SteveRMann/Halloween-2022/Beach Video/Pirate Ship 1.png

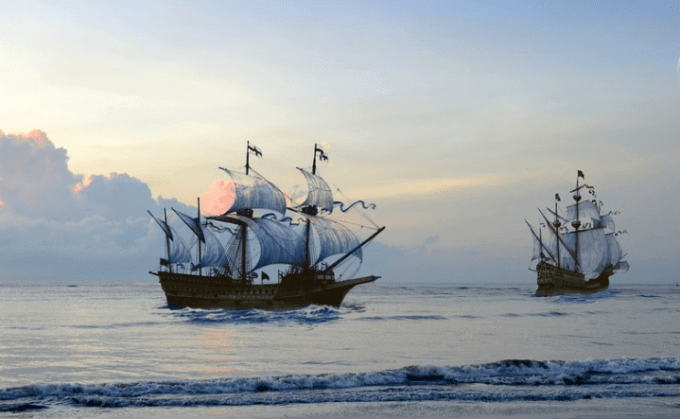
Beach Video/Pirate Ship 1.png
