SteveRMann/Halloween-2022/Beach Video/pirate-ship-blur.png

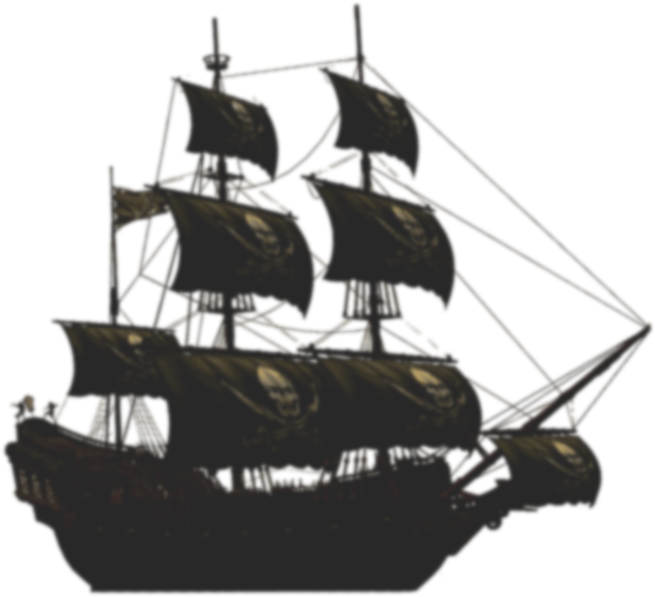
Beach Video/pirate-ship-blur.png
