SteveRMann/Halloween-2022/Beach Video/pirate-ship-transparent.png

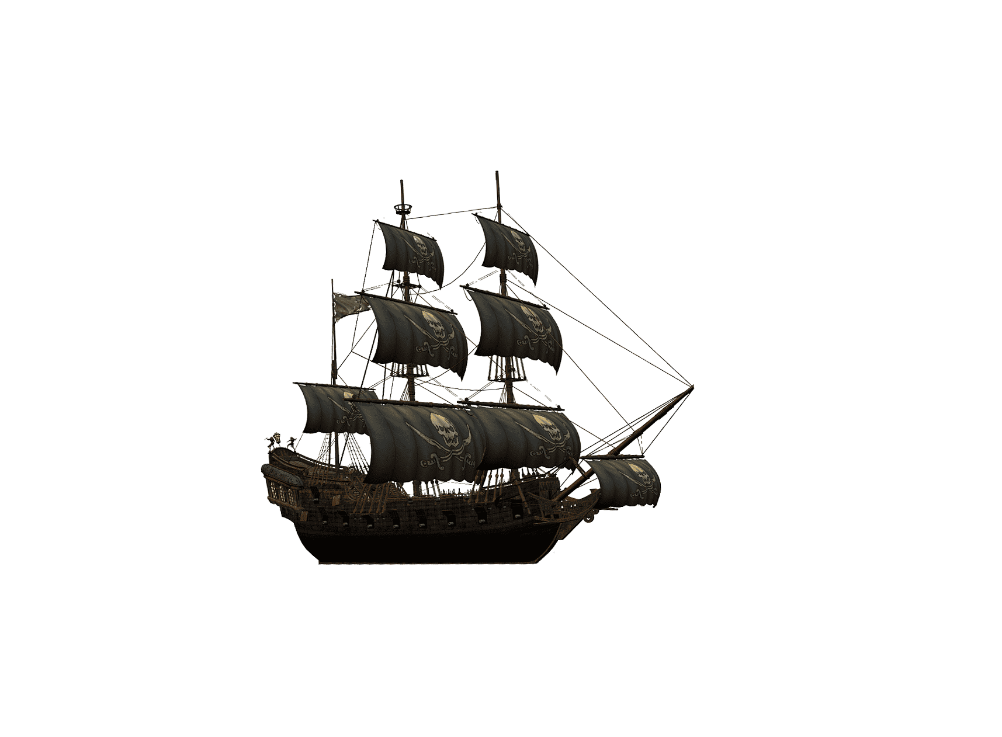
Beach Video/pirate-ship-transparent.png
