SteveRMann/Halloween-2022/Fan/board.jpg

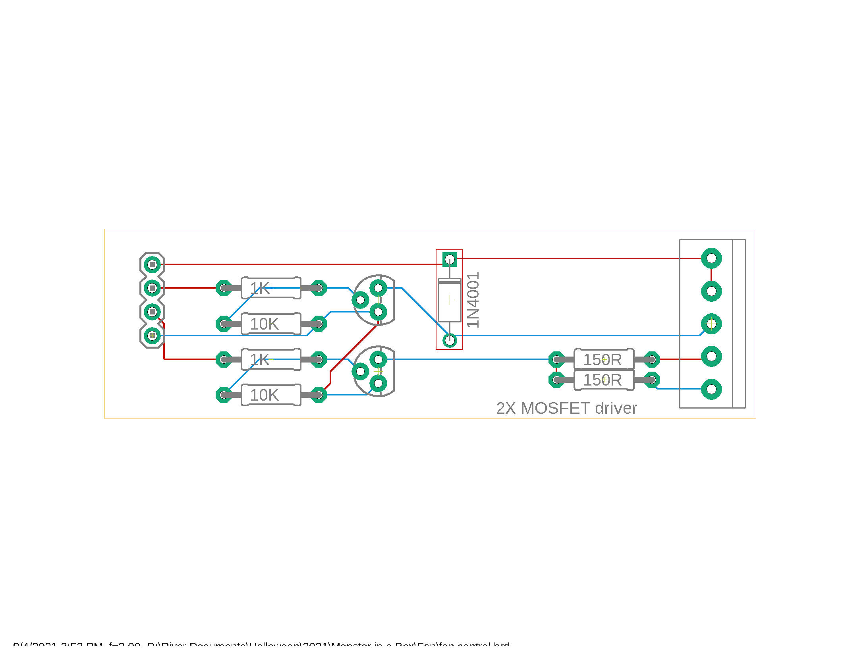
Fan/board.jpg
