SteveRMann/Halloween-2022/Lid Simulator/Fan Control- Monster Box.jpg

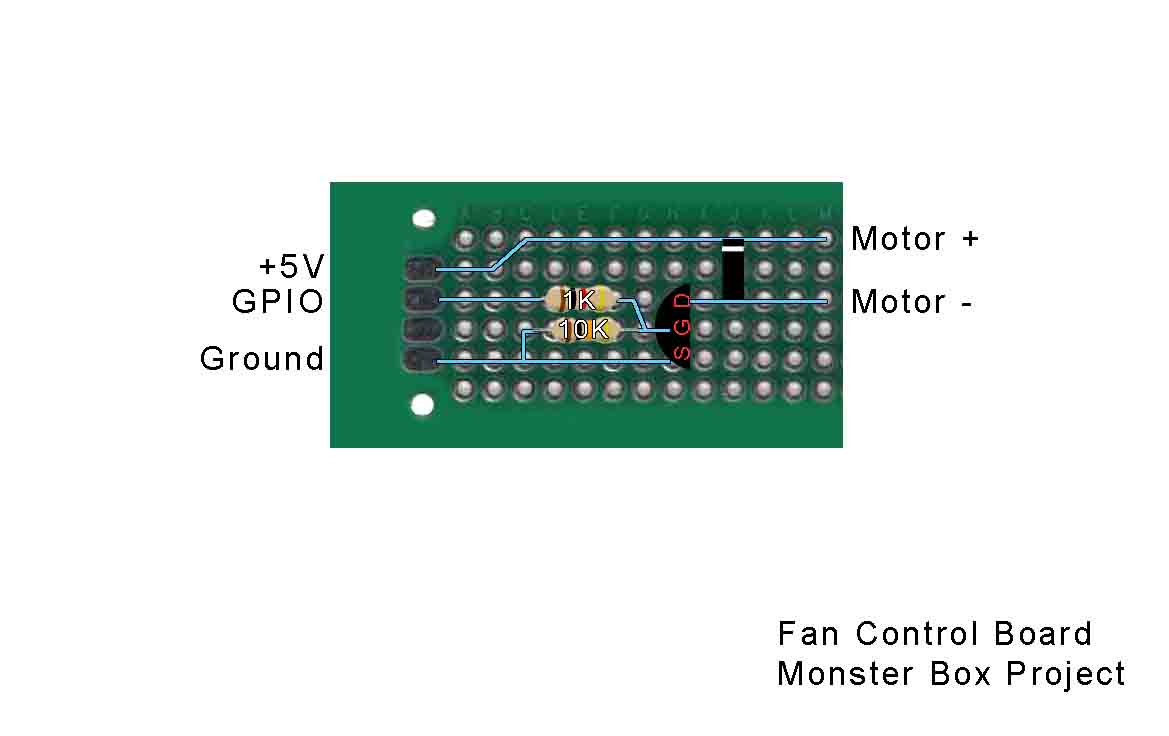
Lid Simulator/Fan Control- Monster Box.jpg
