SteveRMann/Halloween-2022/Lid Simulator/fan control.jpg

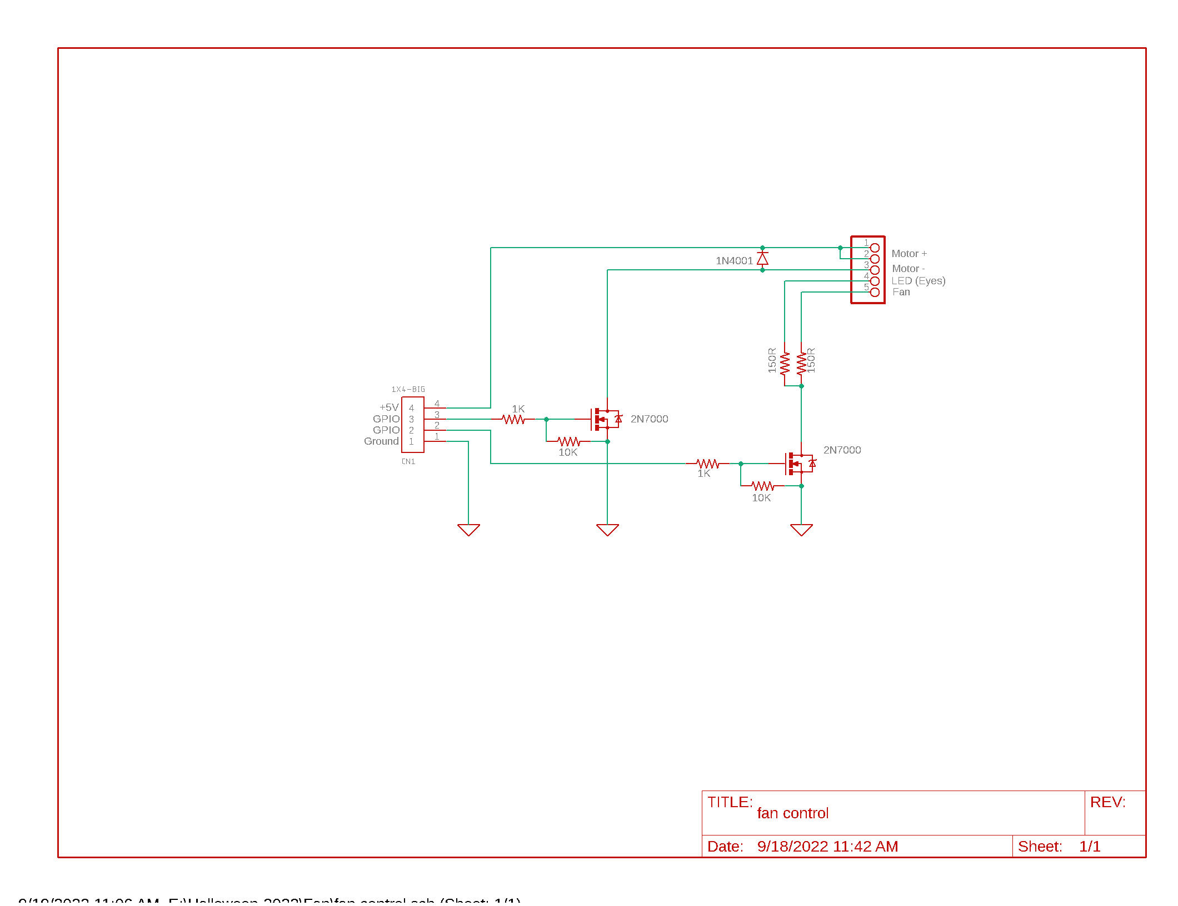
Lid Simulator/fan control.jpg
