SteveRMann/Halloween-2022/Lid Simulator/Lid Simulator Board.jpg

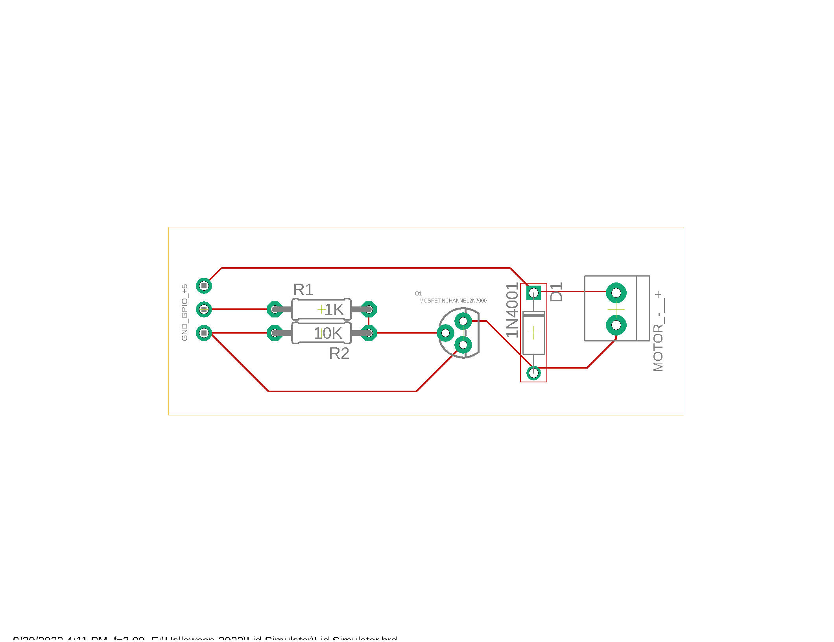
Lid Simulator/Lid Simulator Board.jpg
