SteveRMann/Halloween-2022/Lid Simulator/Trump Grave.jpg

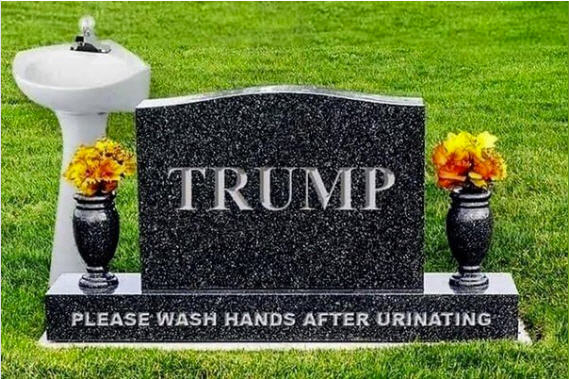
Lid Simulator/Trump Grave.jpg
