SteveRMann/Halloween-2022/MonsterBox/Shield/Shield1.jpg

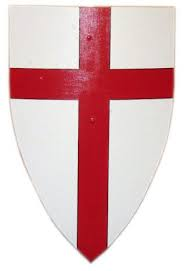
MonsterBox/Shield/Shield1.jpg
