SteveRMann/Halloween-2022/MonsterBox/Shield/Shield2.jpg

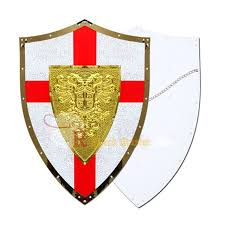
MonsterBox/Shield/Shield2.jpg
