SteveRMann/Halloween-2022/MonsterBox/Shield/Shield3.jpg

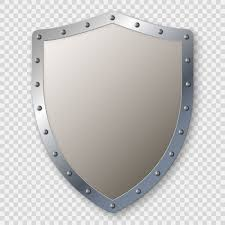
MonsterBox/Shield/Shield3.jpg
