SteveRMann/Halloween-2022/MonsterBox/Shield/shield.jpg

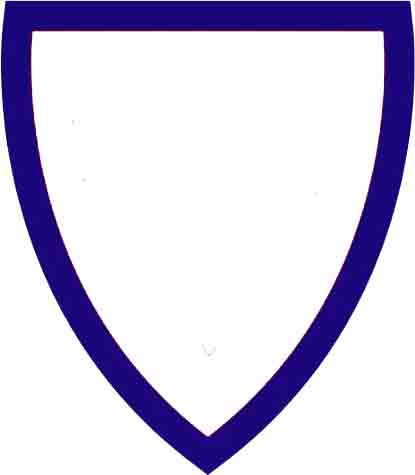
MonsterBox/Shield/shield.jpg
