SteveRMann/Halloween-2022/Shield/DragonHead.jpg

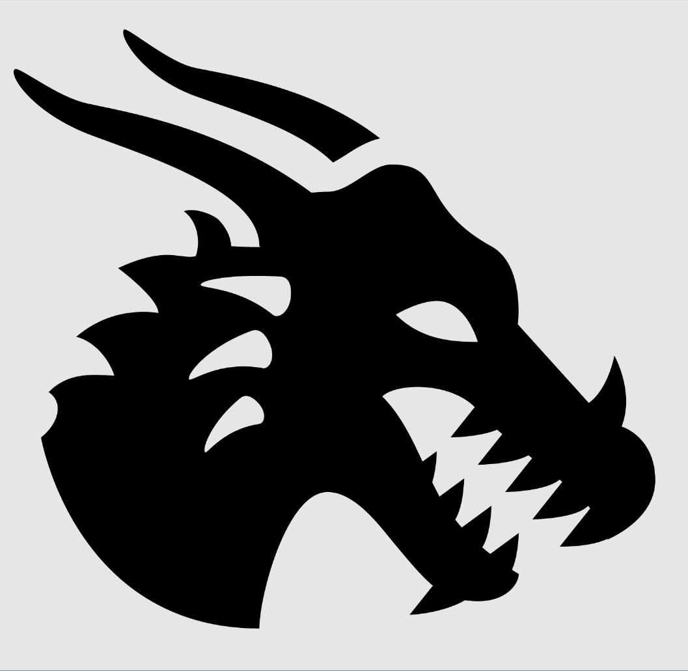
Shield/DragonHead.jpg
