SteveRMann/Halloween-2022/Sounds/DFPlayer/Schematic/20220916_124006.jpg

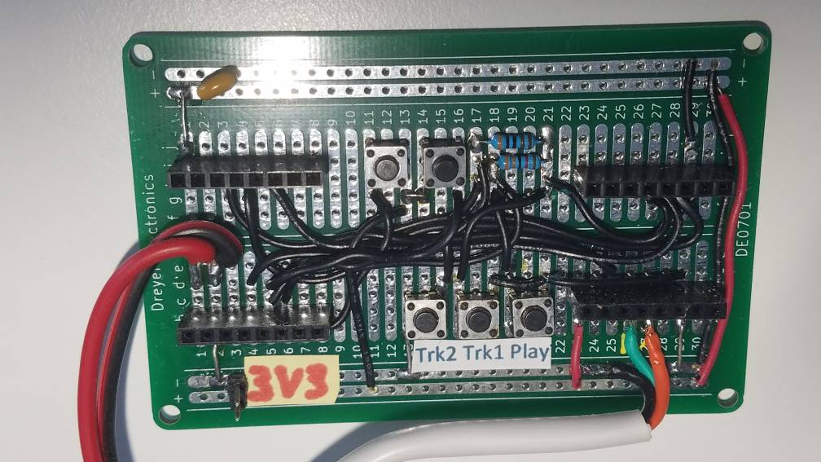
Sounds/DFPlayer/Schematic/20220916_124006.jpg
