SteveRMann/Halloween-2022/Sounds/DFPlayer/Schematic/DFPlayer-Wemos.jpg

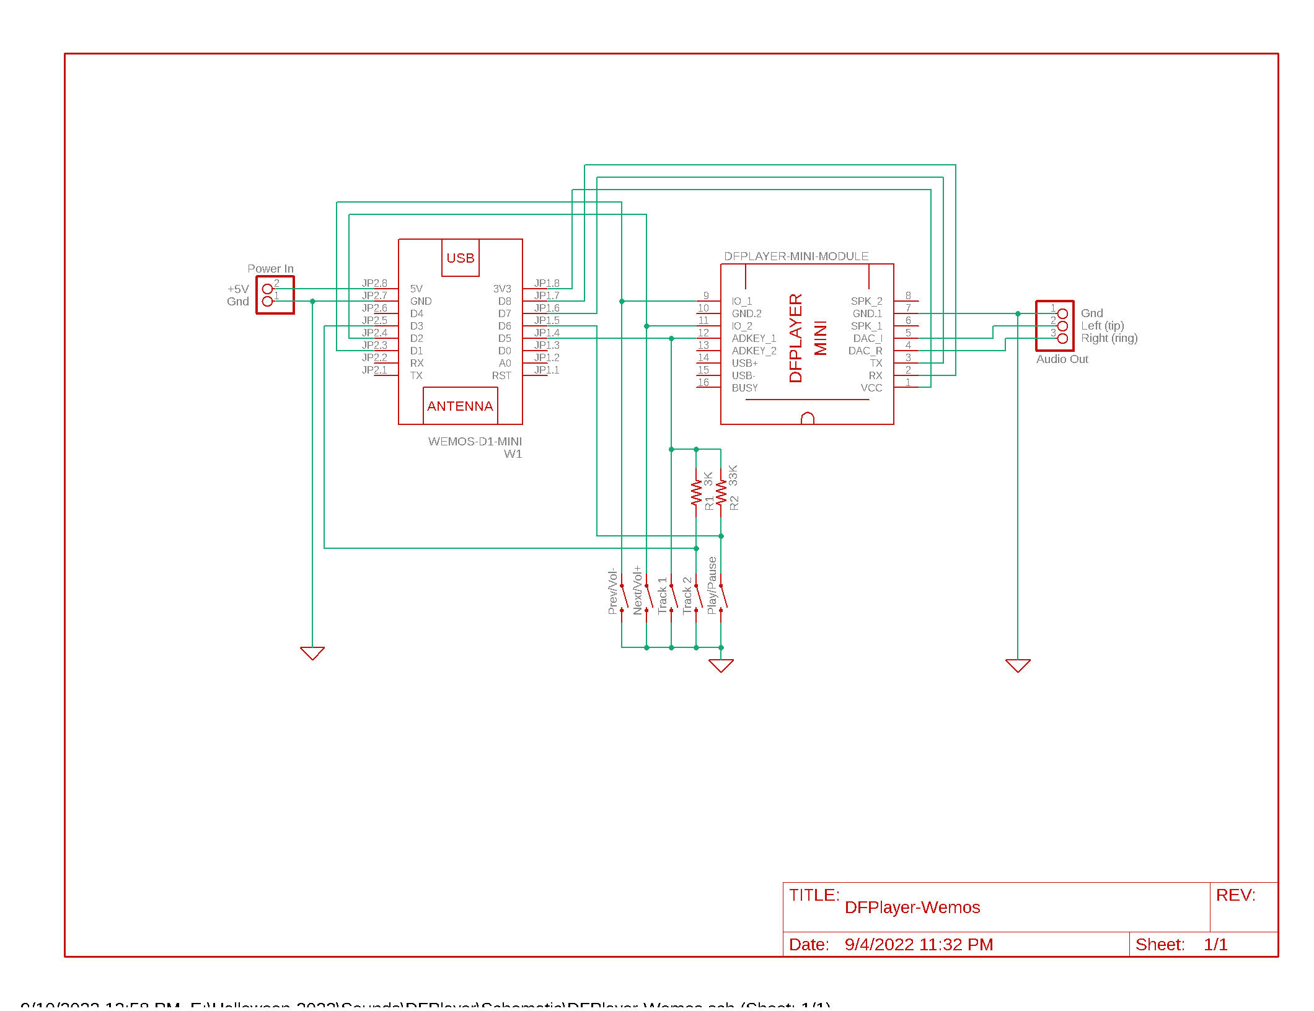
Sounds/DFPlayer/Schematic/DFPlayer-Wemos.jpg
