SteveRMann/Halloween-2022/tail-tentacle hardware/Board photo.jpg

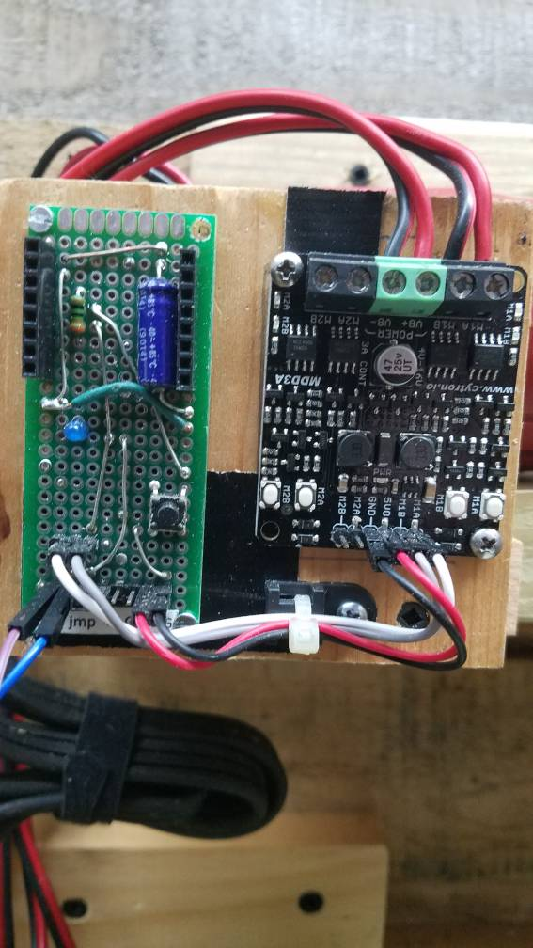
tail-tentacle hardware/Board photo.jpg
