SteveRMann/Halloween-2022/tail-tentacle hardware/tail-tentacle board.jpg

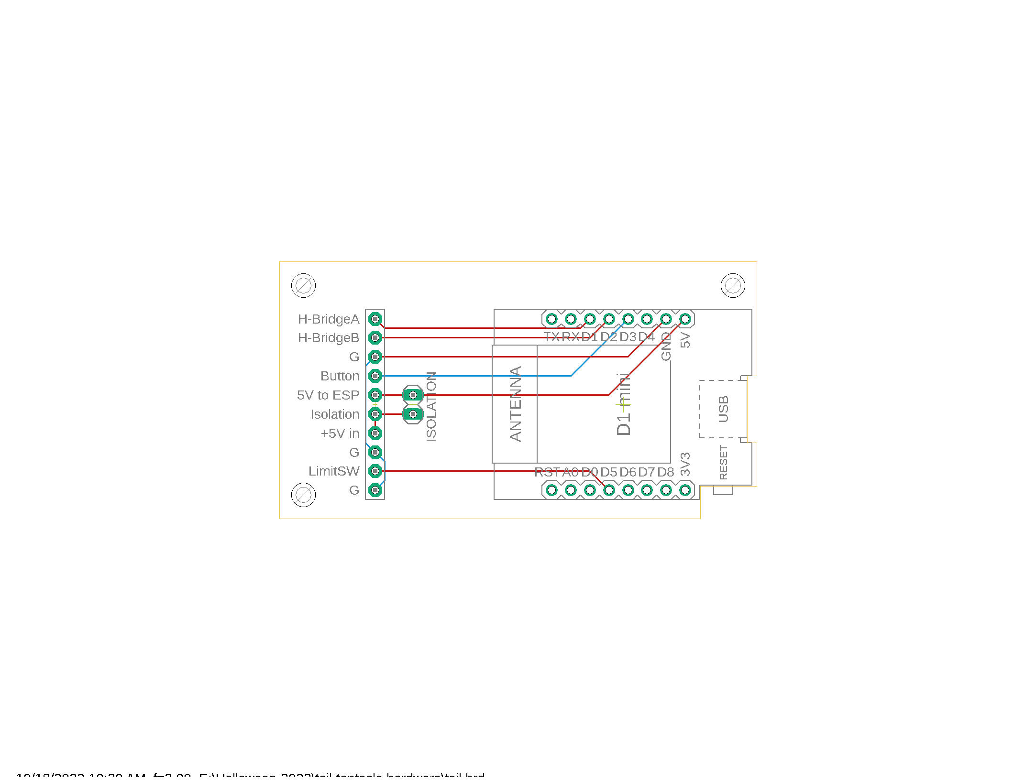
tail-tentacle hardware/tail-tentacle board.jpg
