SteveRMann/Halloween-2022/tail-tentacle hardware/tail-tentacle schematic.jpg

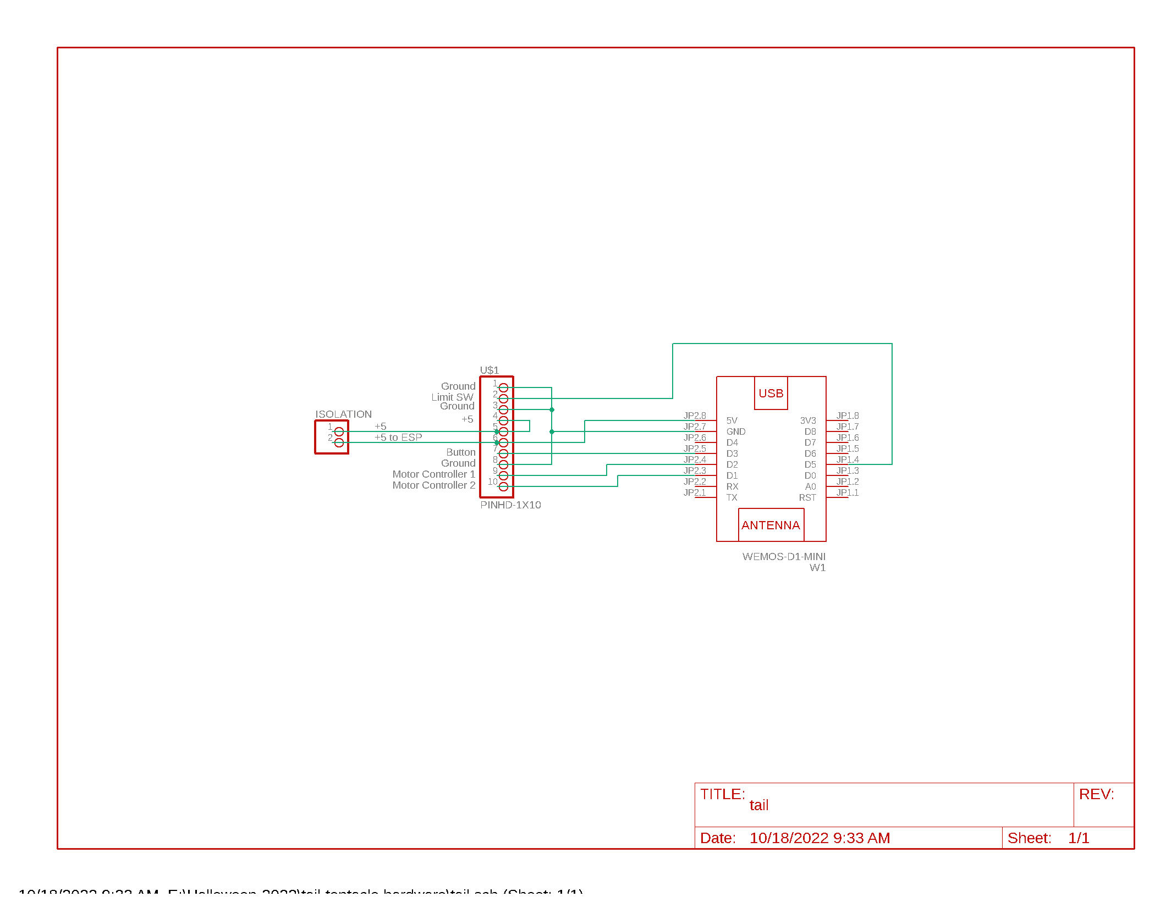
tail-tentacle hardware/tail-tentacle schematic.jpg
