SteveRMann/Halloween-2022/videos/Beach Video/sand.jpg

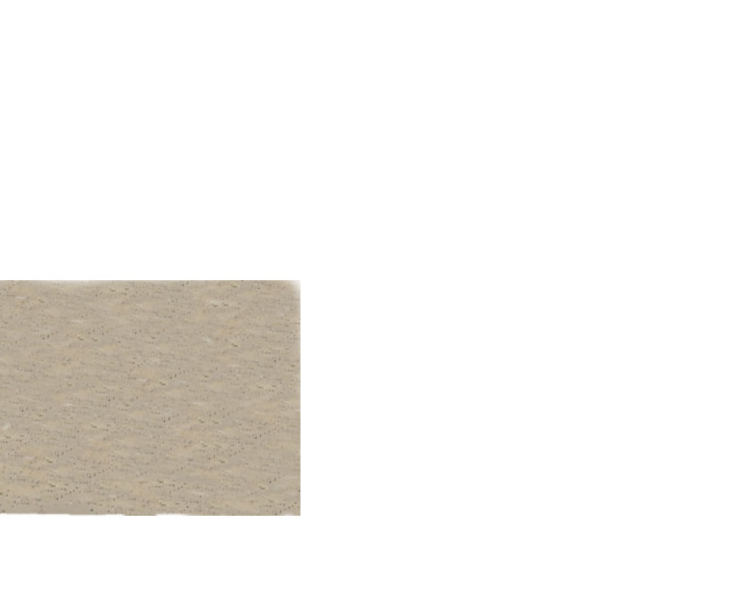
videos/Beach Video/sand.jpg
