SteveRMann/Halloween-2022/videos/Beach Video/sand.png

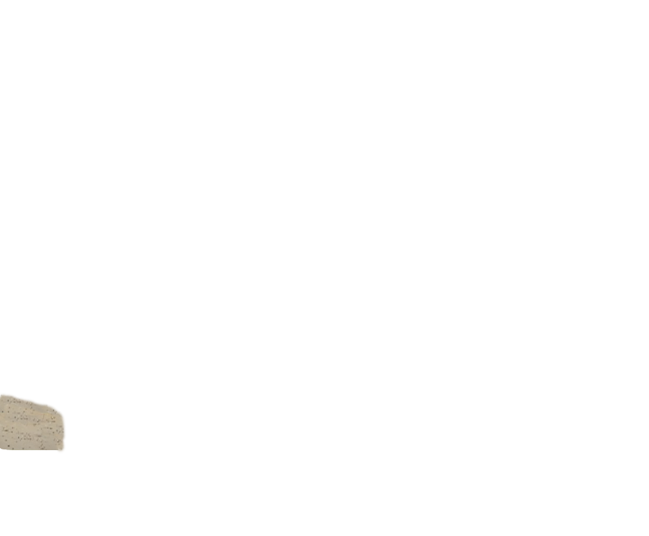
videos/Beach Video/sand.png
