SteveRMann/Halloween-2022/tail-tentacle hardware/Maker Drive- H-Bridge board functions.jpg

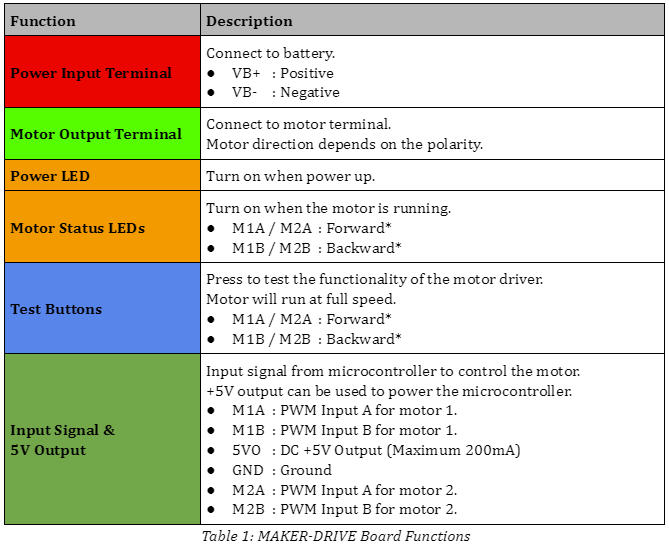
tail-tentacle hardware/Maker Drive- H-Bridge board functions.jpg
