SteveRMann/Halloween-2022/tail-tentacle hardware/Maker Drive- H-Bridge Specifications.jpg

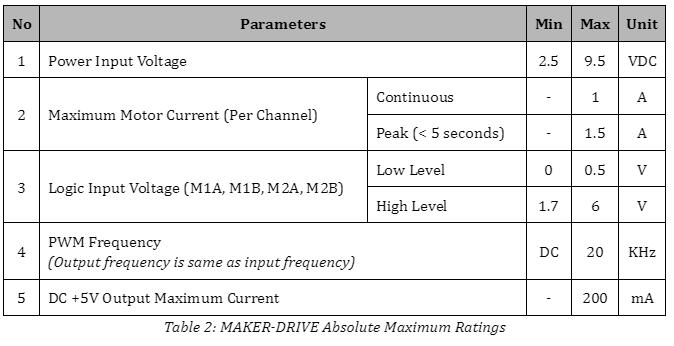
tail-tentacle hardware/Maker Drive- H-Bridge Specifications.jpg
