SteveRMann/Halloween-2022/tail-tentacle hardware/Maker Drive- H-Bridge Truth Table.jpg

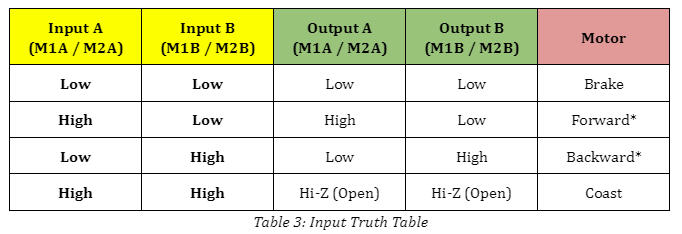
tail-tentacle hardware/Maker Drive- H-Bridge Truth Table.jpg
