SteveRMann/Halloween-2022/Sounds/DFPlayer/Schematic/DFPlayer-Wemos.sch

## EAGLE design Sounds/DFPlayer/Schematic/DFPlayer-Wemos.sch (2021-10-05)

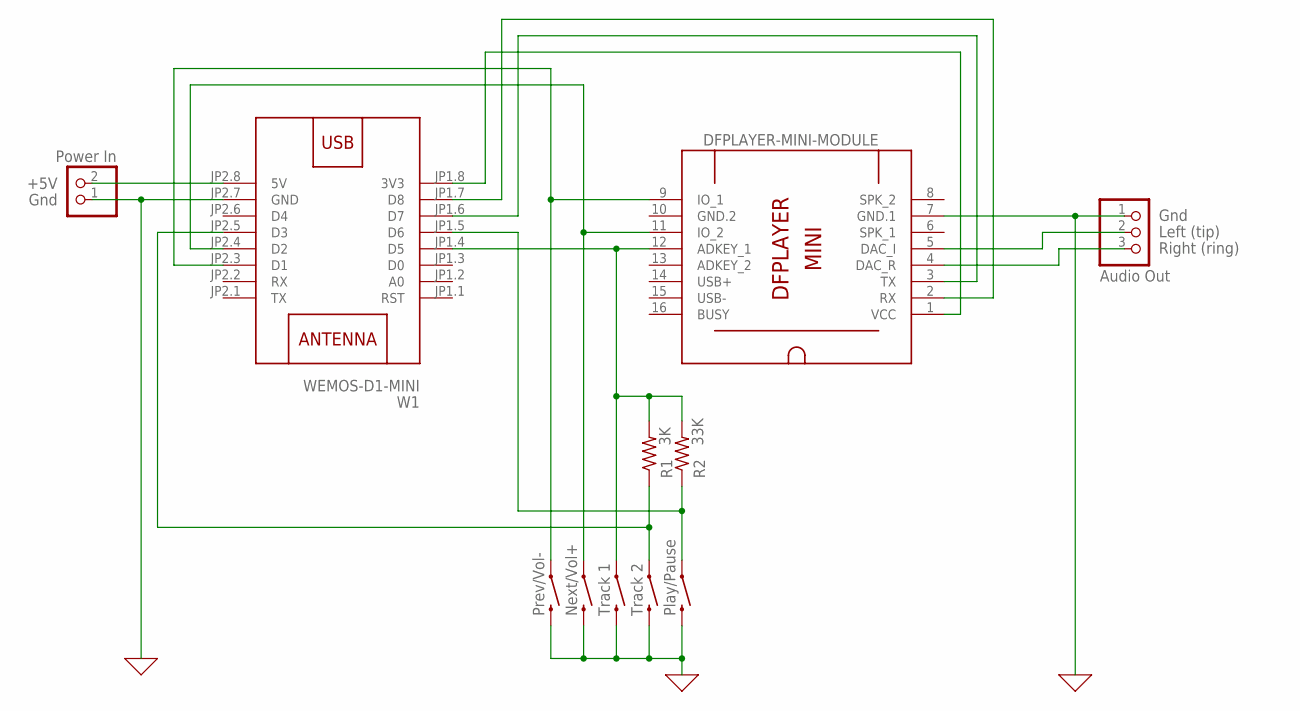
[picture p35: schematic DFPlayer-Wemos.sch]

Parts:
JP2: Audio Out; 1X03
JP3: Power In; 1X02
R1: 3K; 0207/10
R2: 33K; 0207/10
S2, S3, S4, S5, S6: MOMENTARY-SWITCH-SPST-PTH-6.0MM; TACTILE_SWITCH_PTH_6.0MM
U$1: DFPLAYER-MINI-MODULE
W1: WEMOS-D1-MINI

Connections:
0: JP2.1, JP3.1, S2.3 (2), S3.3 (2), S4.3 (2), S5.3 (2), S6.3 (2), U$1.7 (GND.1), W1.JP2.7 (GND)
unnamed: U$1.1 (VCC), W1.JP1.8 (3V3)
unnamed: U$1.3 (TX), W1.JP1.6 (D7)
unnamed: JP3.2, W1.JP2.8 (5V)
unnamed: S2.1, U$1.11 (IO_2), W1.JP2.4 (D2)
unnamed: S3.1, U$1.9 (IO_1), W1.JP2.3 (D1)
unnamed: JP2.2, U$1.5 (DAC_I)
unnamed: R2.1, S5.1, W1.JP1.5 (D6)
unnamed: R1.1, S6.1, W1.JP2.5 (D3)
unnamed: JP2.3, U$1.4 (DAC_R)
unnamed: U$1.2 (RX), W1.JP1.7 (D8)
unnamed: R1.2, R2.2, S4.1, U$1.12 (ADKEY_1), W1.JP1.4 (D5)

Notes on the sheet:
Next/Vol+
Prev/Vol-
Track 1
Track 2
Play/Pause
Gnd
Left (tip)
Right (ring)
+5V
