SteveRMann/Halloween-2022/MonsterBox/motorControl-doorV6/ota.ino

void start_OTA() {
  /*
    Make sure you include at the start of the sketch:
    //--------------- OTA declarations ---------------
    #include <ArduinoOTA.h>
    //--------------- End of OTA declarations ---------------

    Start loop() with:
    ArduinoOTA.handle();

    // --------------- Typical setup ---------------
    void setup() {
      beginSerial();
      setup_wifi();
      start_OTA();      // Follows setupWifi()
    }

  */

  //Hostname defaults to esp8266-[MAC address]
  ArduinoOTA.setHostname(hostName);                 // hostName is generated in 'setup_wifi'.
  ArduinoOTA.onStart([]() {
    String type;
    if (ArduinoOTA.getCommand() == U_FLASH) {
      type = "sketch";
    } else { // U_SPIFFS
      type = "filesystem";
    }

    // NOTE: if updating SPIFFS this would be the place to unmount SPIFFS using SPIFFS.end()
    Serial.println("Start updating " + type);
  });
  ArduinoOTA.onEnd([]() {
    Serial.println("\nEnd");
  });
  ArduinoOTA.onProgress([](unsigned int progress, unsigned int total) {
    Serial.printf("Progress: %u%%\r", (progress / (total / 100)));
  });
  ArduinoOTA.onError([](ota_error_t error) {
    Serial.printf("Error[%u]: ", error);
    if (error == OTA_AUTH_ERROR) {
      Serial.println("Auth Failed");
    } else if (error == OTA_BEGIN_ERROR) {
      Serial.println("Begin Failed");
    } else if (error == OTA_CONNECT_ERROR) {
      Serial.println("Connect Failed");
    } else if (error == OTA_RECEIVE_ERROR) {
      Serial.println("Receive Failed");
    } else if (error == OTA_END_ERROR) {
      Serial.println("End Failed");
    }
  });
  ArduinoOTA.begin();
  Serial.println("OTA Ready");

}
