SteveRMann/Halloween-2022/src/Lid/wifiMulti.ino

void setup_wifiMulti() {
  /*
    In the main program, include:
      //--------------- WiFiMulti declarations ---------------
      #include <ESP8266WiFiMulti.h>
      ESP8266WiFiMulti wifiMulti;

      // WiFi connect timeout per AP. Increase when connecting takes longer.
      const uint32_t connectTimeoutMs = 5000;

      // setup_wifi vars
      char macBuffer[24];       // Holds the last three digits of the MAC, in hex.
      char hostNamePrefix[] = hostPrefix;
      char hostName[12];        // Holds hostNamePrefix + the last three bytes of the MAC address.

    And in setup:
      setup_wifiMulti();
  */

 /// const uint32_t connectTimeoutMs = 5000;
  ///byte mac[6];                      //// the MAC address of your Wifi shield

  Serial.println(F("Connecting to WiFi"));

  // Don't save WiFi configuration in flash - optional
  WiFi.persistent(false);

  // Set WiFi to station mode
  WiFi.mode(WIFI_STA);

  // Register multi WiFi networks
  // Defined in kaywinnet.h
///#ifndef Kaywinnet
#include "Kaywinnet.h"
///#endif
  wifiMulti.addAP("Naboo", NABOO_PASSWORD);
  wifiMulti.addAP("Serenity", SERENITY_PASSWORD);
  wifiMulti.addAP("Miranda", MIRANDA_PASSWORD);
  wifiMulti.addAP("Kaywinnet", KAYWINNET_PASSWORD);

  blueTicker.attach(0.1, blueTick);          // Start blueTick() while we connect

  if (wifiMulti.run(connectTimeoutMs) == WL_CONNECTED) {
    blueTicker.detach();                     // Stop blueTick()
    Serial.print(F("WiFi connected: "));
    Serial.println(WiFi.SSID());
    Serial.print(F("MAC Address: "));
    Serial.println(WiFi.macAddress());
    Serial.print(F("IP Address: "));
    Serial.println(WiFi.localIP());
    Serial.print(F("Hostname: "));
    Serial.println(WiFi.hostname());
    long rssi = WiFi.RSSI();
    Serial.print("RSSI: ");
    Serial.println(rssi);
  } else {
    Serial.println(F("WiFi not connected!"));
  }

/*
  // Get the last three numbers of the mac address.
  // "4C:11:AE:0D:83:86" becomes "0D8386" in macBuffer.
  WiFi.macAddress(mac);
  snprintf(macBuffer, sizeof(macBuffer), "%02X%02X%02X", mac[3], mac[4], mac[5]);

  // Build hostNamePrefix + last three bytes of the MAC address.
  strcpy(hostName, hostNamePrefix);
  strcat(hostName, macBuffer);

  //Serial.print(F("hostName = \""));
  //Serial.print(hostName);
  //Serial.println(F("\""));
*/
}
